uwrov/NanoFloat2.0-nanOS/MATE-Competition/taskconfig.h

#ifndef TASKCONFIG_H
#define TASKCONFIG_H

const long ENCODER_MIN_COUNT = 0;
const long ENCODER_MAX_COUNT = 195000;

const float MIN_DEPTH = 0.0;
const float MAX_DEPTH = 4.0;

const unsigned long HOLD_TIME = 30000;

#endif
