uwrov/NanoFloat2.0-nanOS/MATE-Competition/testconfig.h

#ifndef TESTCONFIG_H
#define TESTCONFIG_H

const long ENCODER_MIN_COUNT = 0;
const long ENCODER_MAX_COUNT = 195000;

const float MIN_DEPTH_M = 0.0;
const float MAX_DEPTH_M = 4.0;

const unsigned long MAX_MOTOR_TIME_MS = 240000; // In milliseconds - 4 minutes

#endif
